eliddell1/FistBump/scripts/FistBump/random_colors.py

#!/usr/bin/env python

import random
import time

import blinkt

blinkt.set_clear_on_exit()

while True:
    pixels = random.sample(range(blinkt.NUM_PIXELS), random.randint(1, 5))
    for i in range(blinkt.NUM_PIXELS):
        if i in pixels:
            blinkt.set_pixel(i, random.randint(0, 255), random.randint(0, 255), random.randint(0, 255), .1)
        else:
            blinkt.set_pixel(i, 0, 0, 0)
    blinkt.show()
    time.sleep(0.05)
